NBER08/CanSat_Devboard/HTML/images/cat_pdf_drill_map_CanSat_Devboard-PTH_drill_map.png

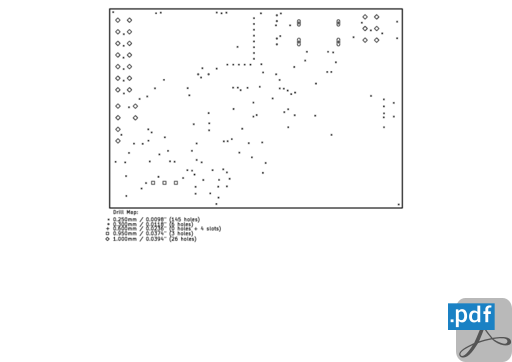
HTML/images/cat_pdf_drill_map_CanSat_Devboard-PTH_drill_map.png
