NBER08/CanSat_Devboard/HTML/images/cat_png_3d_viewer_bottom_CanSat_Devboard-bottom.png

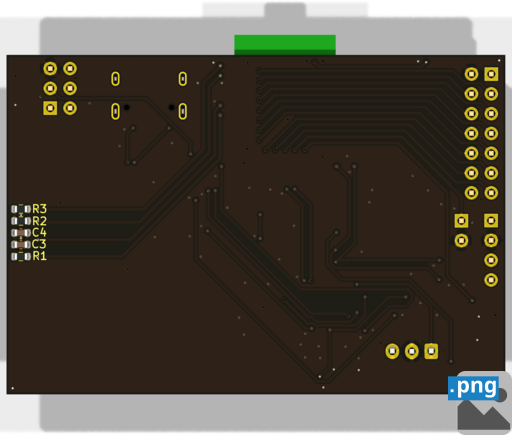
HTML/images/cat_png_3d_viewer_bottom_CanSat_Devboard-bottom.png
