NBER08/CanSat_Devboard/Manufacturing/Fabrication/CanSat_Devboard-fabrication.pdf

# Top Fabrication (Scale 1:1)

# CanSat Devboard Fabrication Document

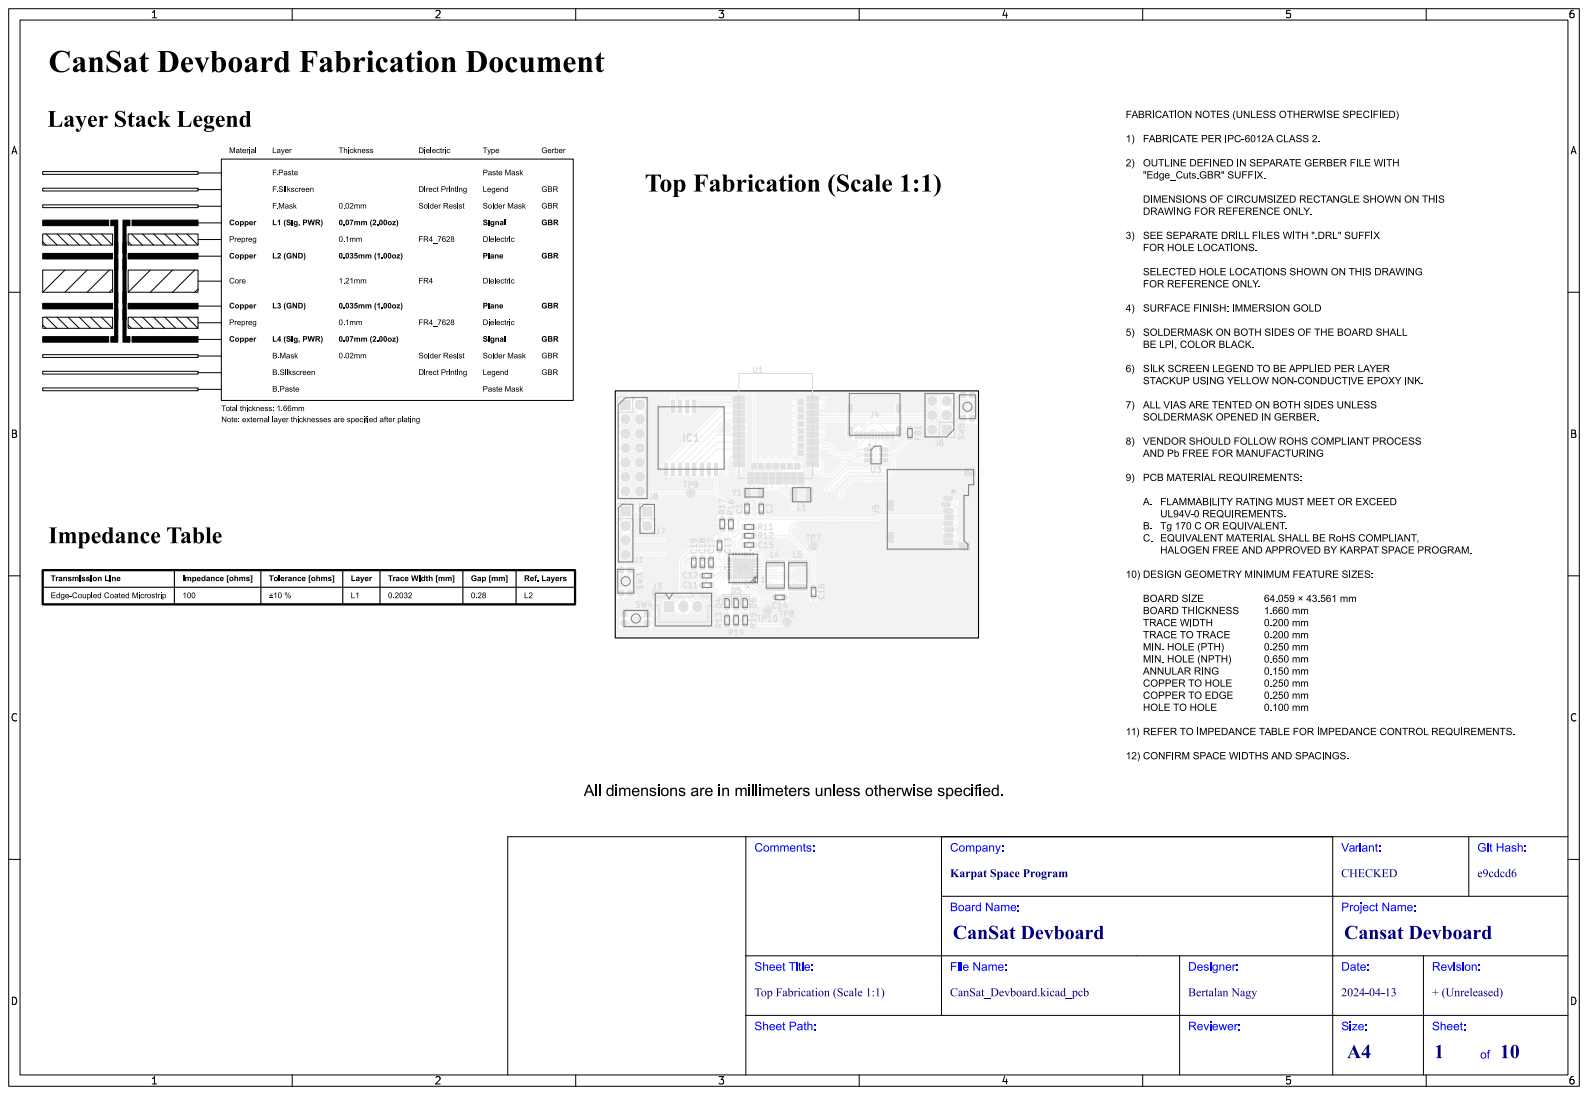
[picture p10: page 1]

# Bottom Fabrication (Scale 1:1)

# CanSat Devboard Fabrication Document

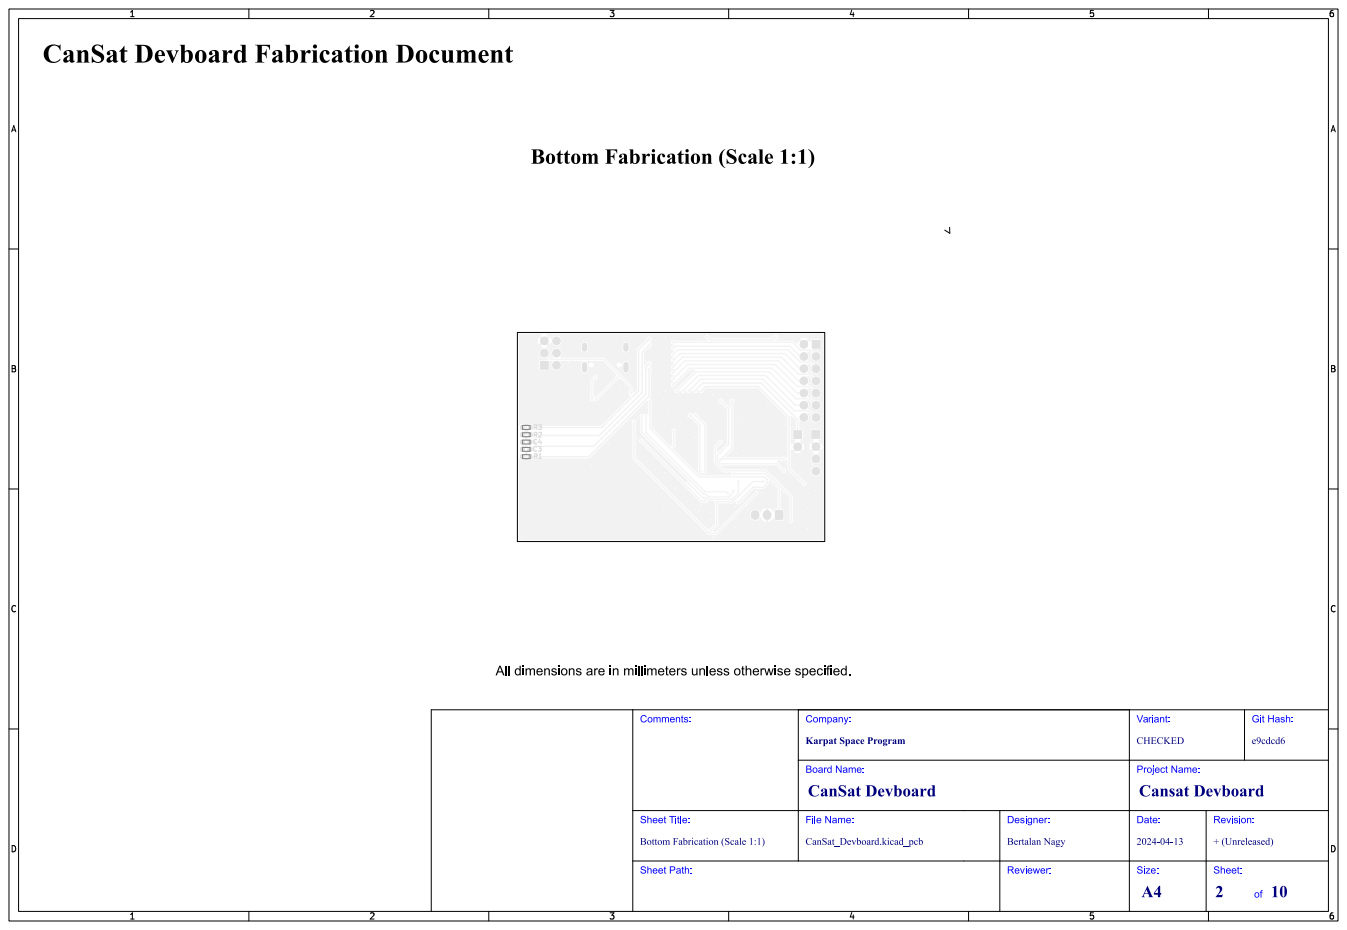
[picture p11: page 2]
Git; Hash:; e9cdcd6; Comments:; Sheet Path:; Sheet Title:; File Name:; CanSat Devboard; Cansat Devboard; Company:; CHECKED; Variant:; Board Name:; CanSat_Devboard.kicad_pcb; Bertalan Nagy; Designer:; Reviewer:; Project Name:; Date:; + (Unreleased); Revision:; Size:; Sheet:

Karpat Space Program

Bottom Fabrication (Scale 1:1)

# Drill Drawing L1 - L4 (Scale 1:1)

# CanSat Devboard Fabrication Document

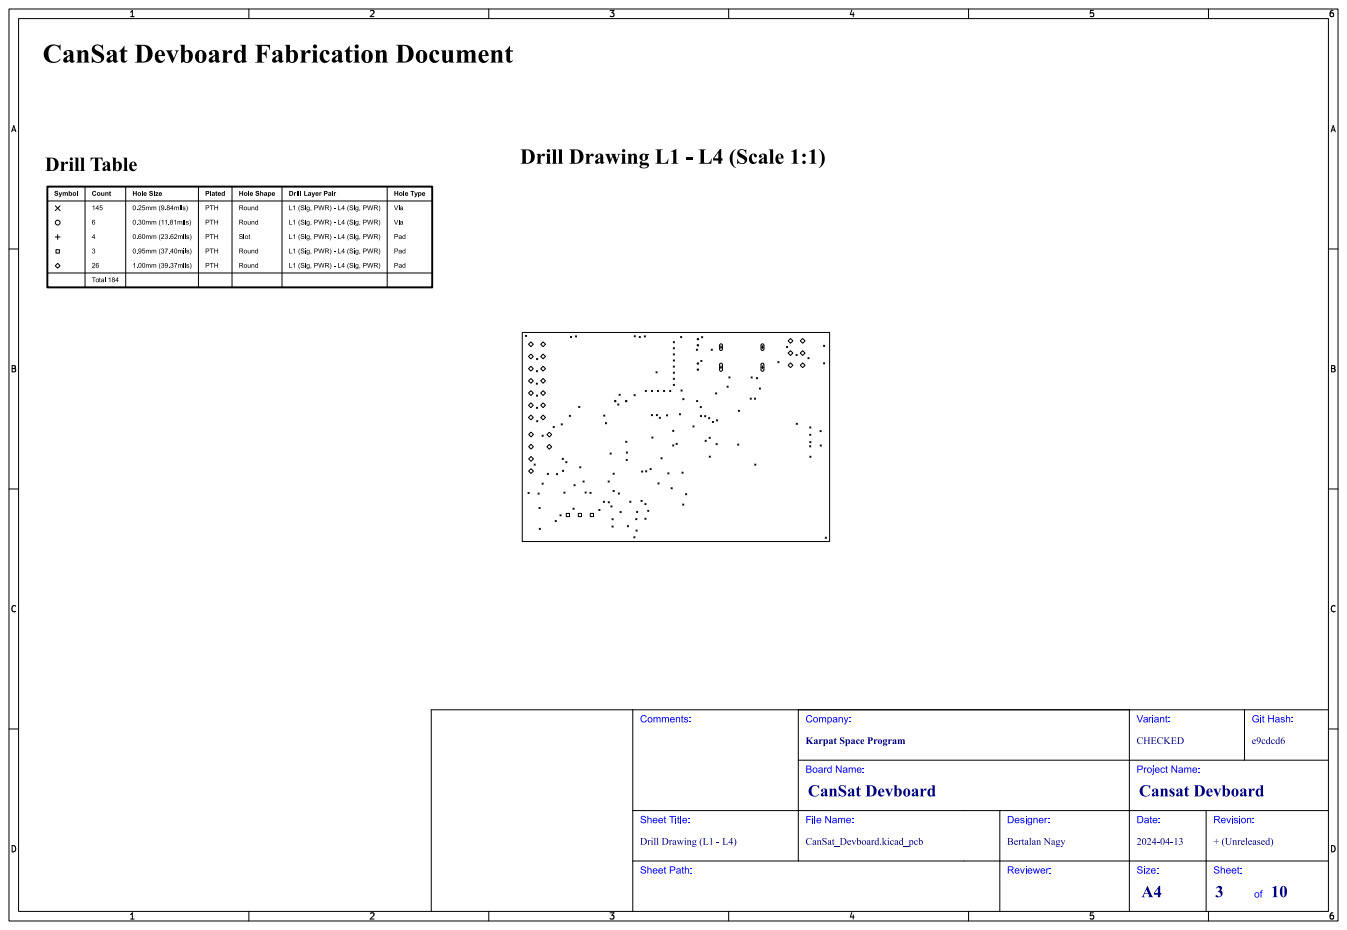
[picture p12: page 3]
Git; Hash:; e9cdcd6; Comments:; Drill Drawing (L1 - L4); Sheet Path:; Sheet Title:; File Name:; CanSat Devboard; Cansat Devboard; Company:; CHECKED; Variant:; Board Name:; CanSat_Devboard.kicad_pcb; Bertalan Nagy; Designer:; Reviewer:; Project Name:; Date:; + (Unreleased); Revision:; Size:; Sheet:

Karpat Space Program

# Drill Drawing L1 - L4 (Scale 1:1)

# CanSat Devboard Fabrication Document

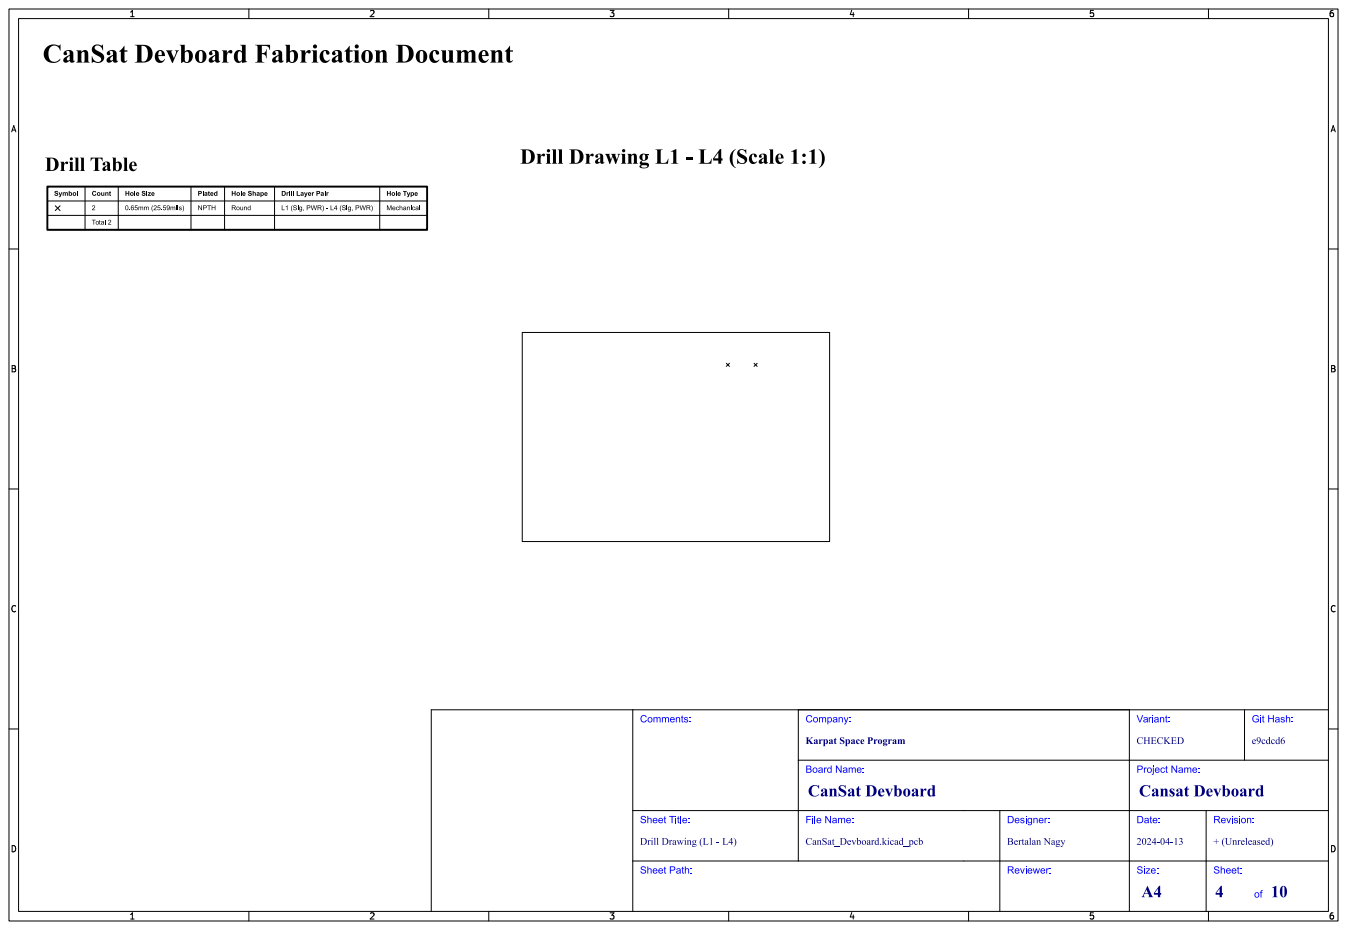
[picture p13: page 4]
Git; Hash:; e9cdcd6; Comments:; Drill Drawing (L1 - L4); Sheet Path:; Sheet Title:; File Name:; CanSat Devboard; Cansat Devboard; Company:; CHECKED; Variant:; Board Name:; CanSat_Devboard.kicad_pcb; Bertalan Nagy; Designer:; Reviewer:; Project Name:; Date:; + (Unreleased); Revision:; Size:; Sheet:

Karpat Space Program

# Top Test Points (Scale 1:1)

# CanSat Devboard Fabrication Document

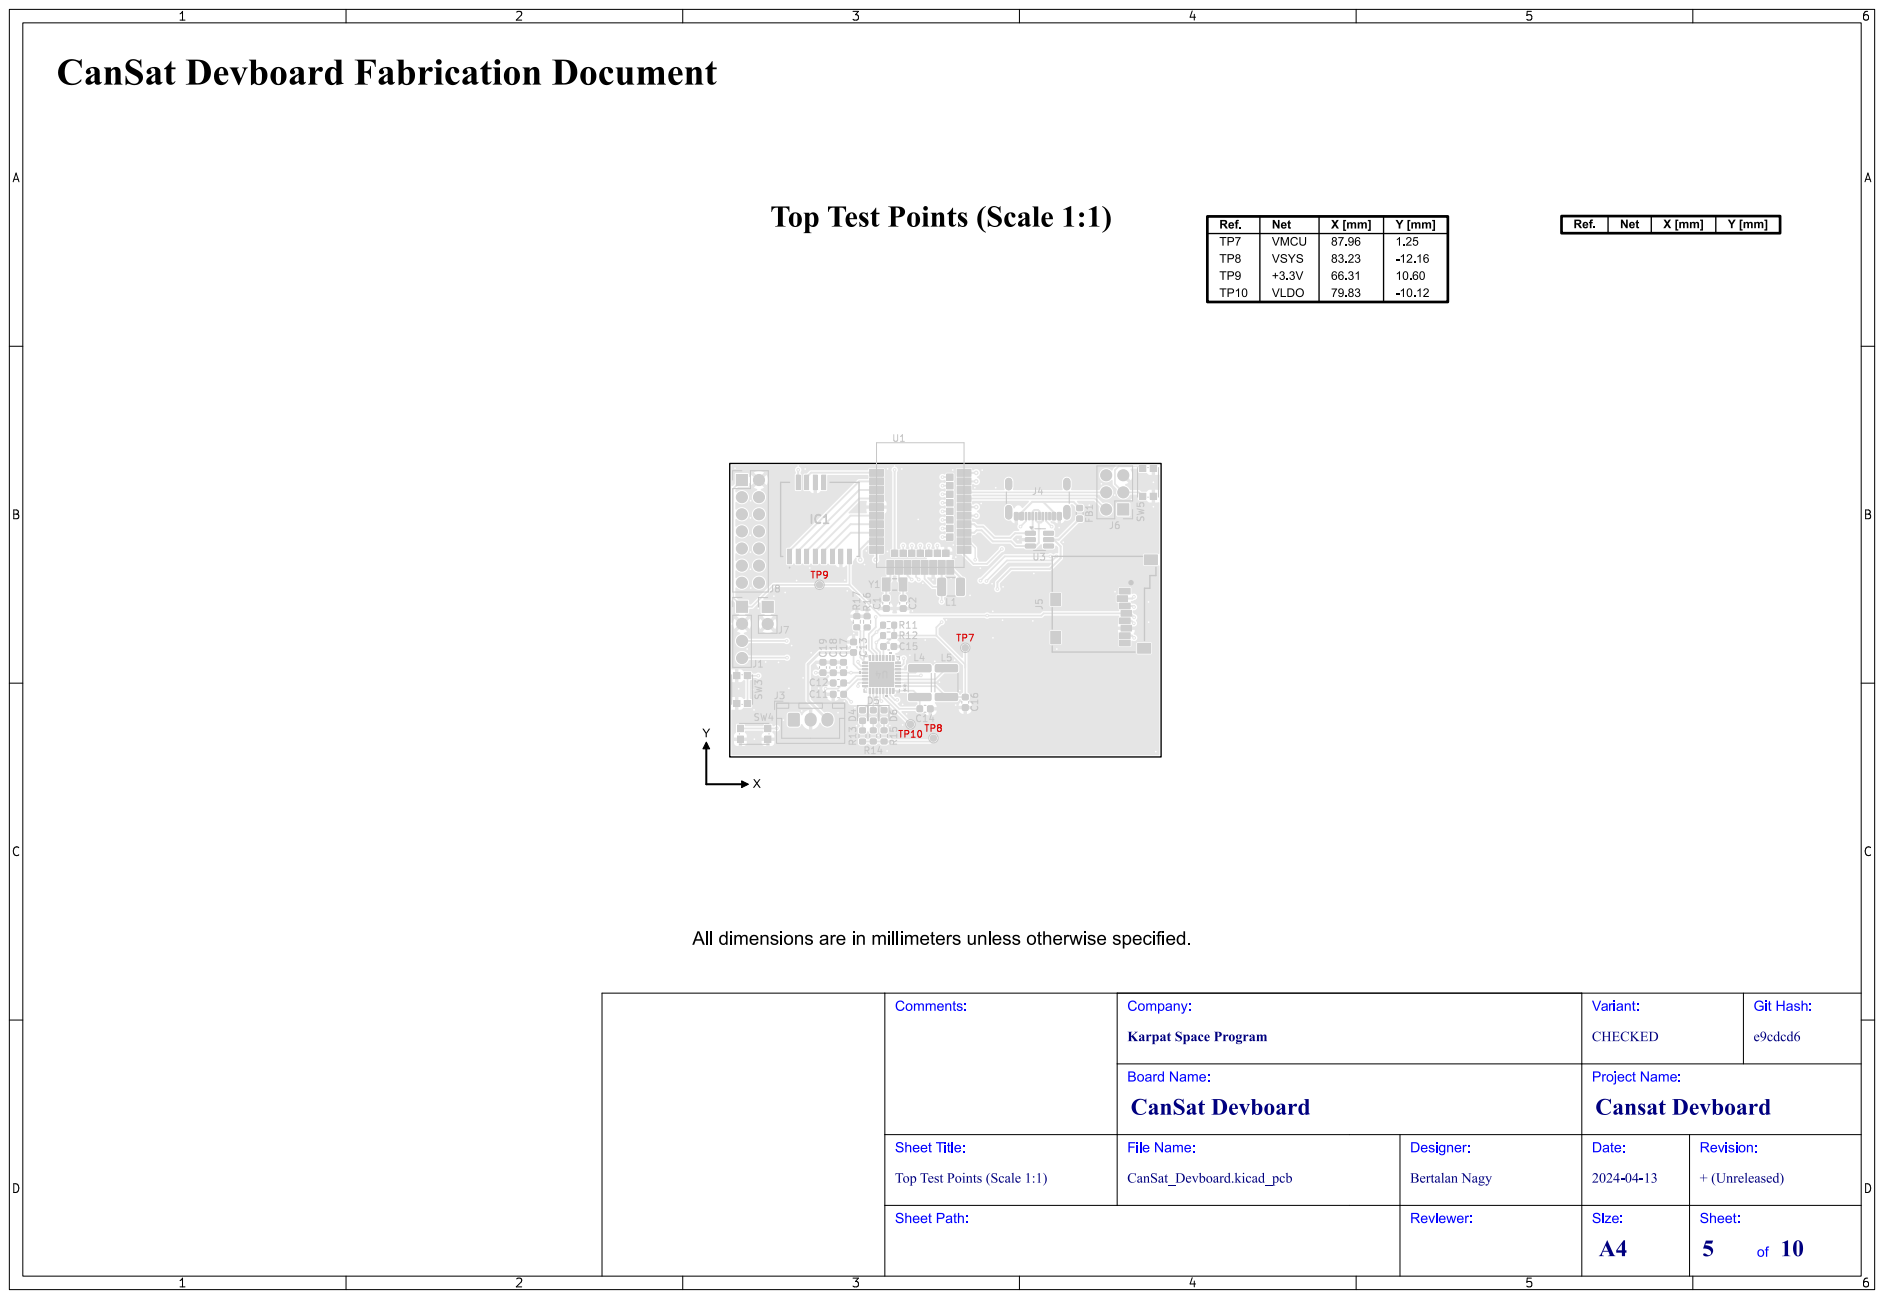
[picture p14: page 5]

Top Test Points (Scale 1:1)

# Bottom Test Points (Scale 1:1)

# CanSat Devboard Fabrication Document

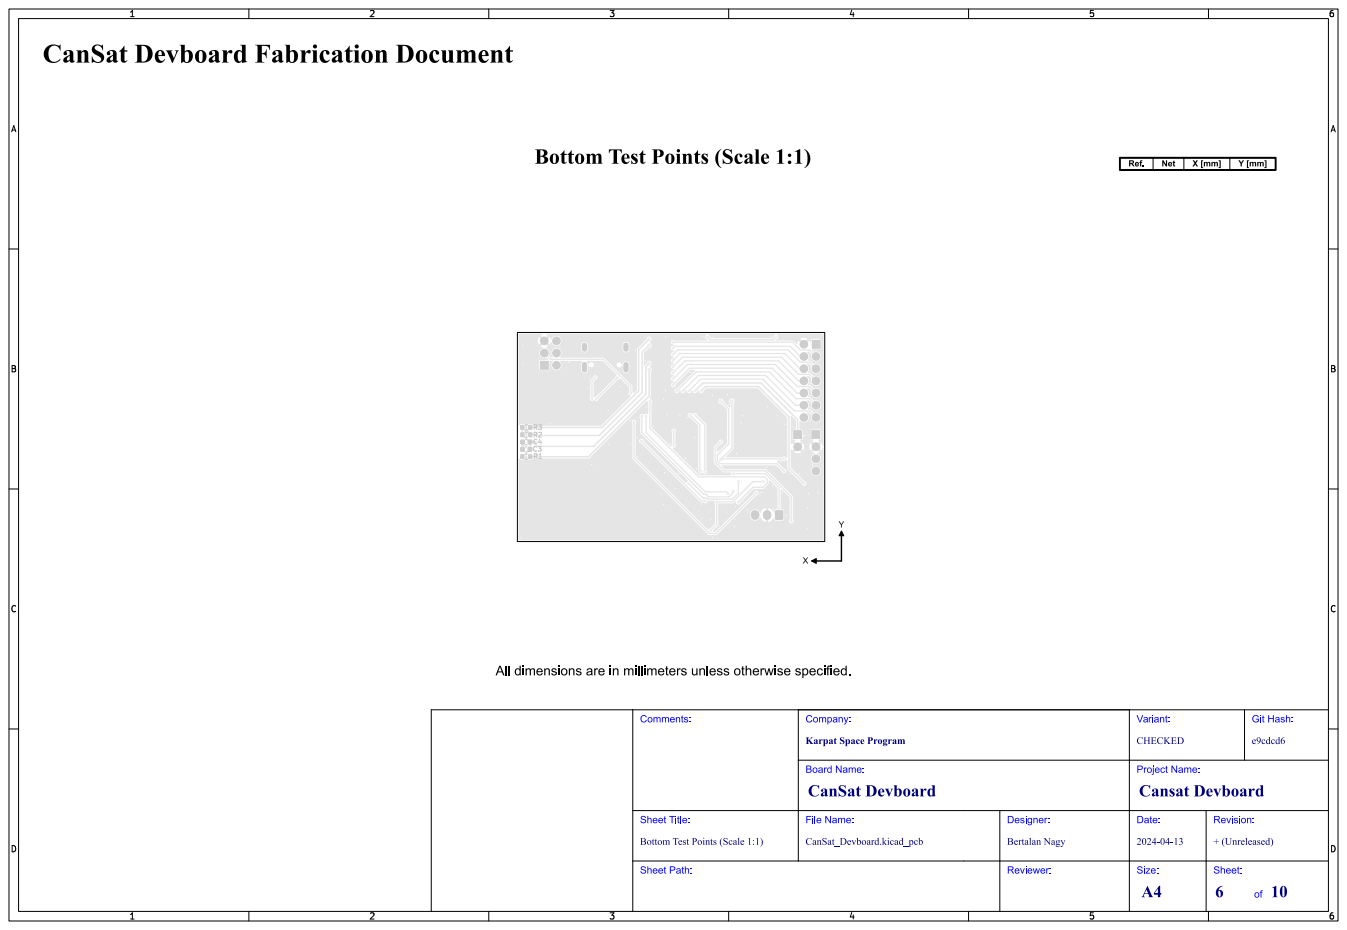
[picture p15: page 6]
Git; Hash:; e9cdcd6; Comments:; Sheet Path:; Sheet Title:; File Name:; CanSat Devboard; Cansat Devboard; Company:; CHECKED; Variant:; Board Name:; CanSat_Devboard.kicad_pcb; Bertalan Nagy; Designer:; Reviewer:; Project Name:; Date:; + (Unreleased); Revision:; Size:; Sheet:

Karpat Space Program

Bottom Test Points (Scale 1:1)

# L1 (Sig, PWR) (Scale 1:1)

# CanSat Devboard Fabrication Document

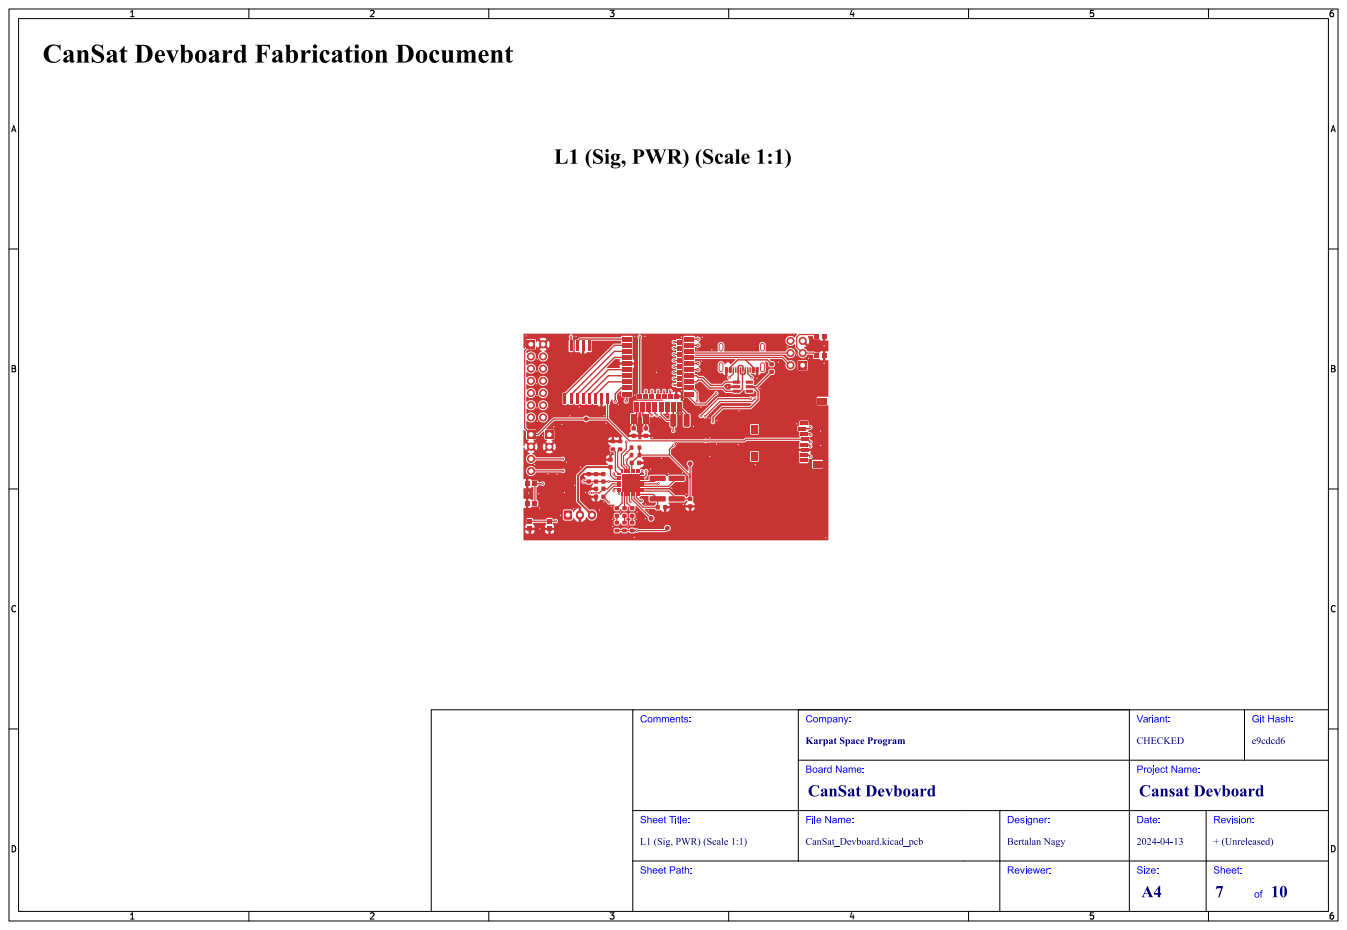
[picture p16: page 7]
Git; Hash:; e9cdcd6; Comments:; Sheet Path:; Sheet Title:; File Name:; CanSat Devboard; Cansat Devboard; Company:; CHECKED; Variant:; Board Name:; CanSat_Devboard.kicad_pcb; Bertalan Nagy; Designer:; Reviewer:; Project Name:; Date:; + (Unreleased); Revision:; Size:; Sheet:

Karpat Space Program

L1 (Sig, PWR) (Scale 1:1)

# L2 (GND) (Scale 1:1)

# CanSat Devboard Fabrication Document

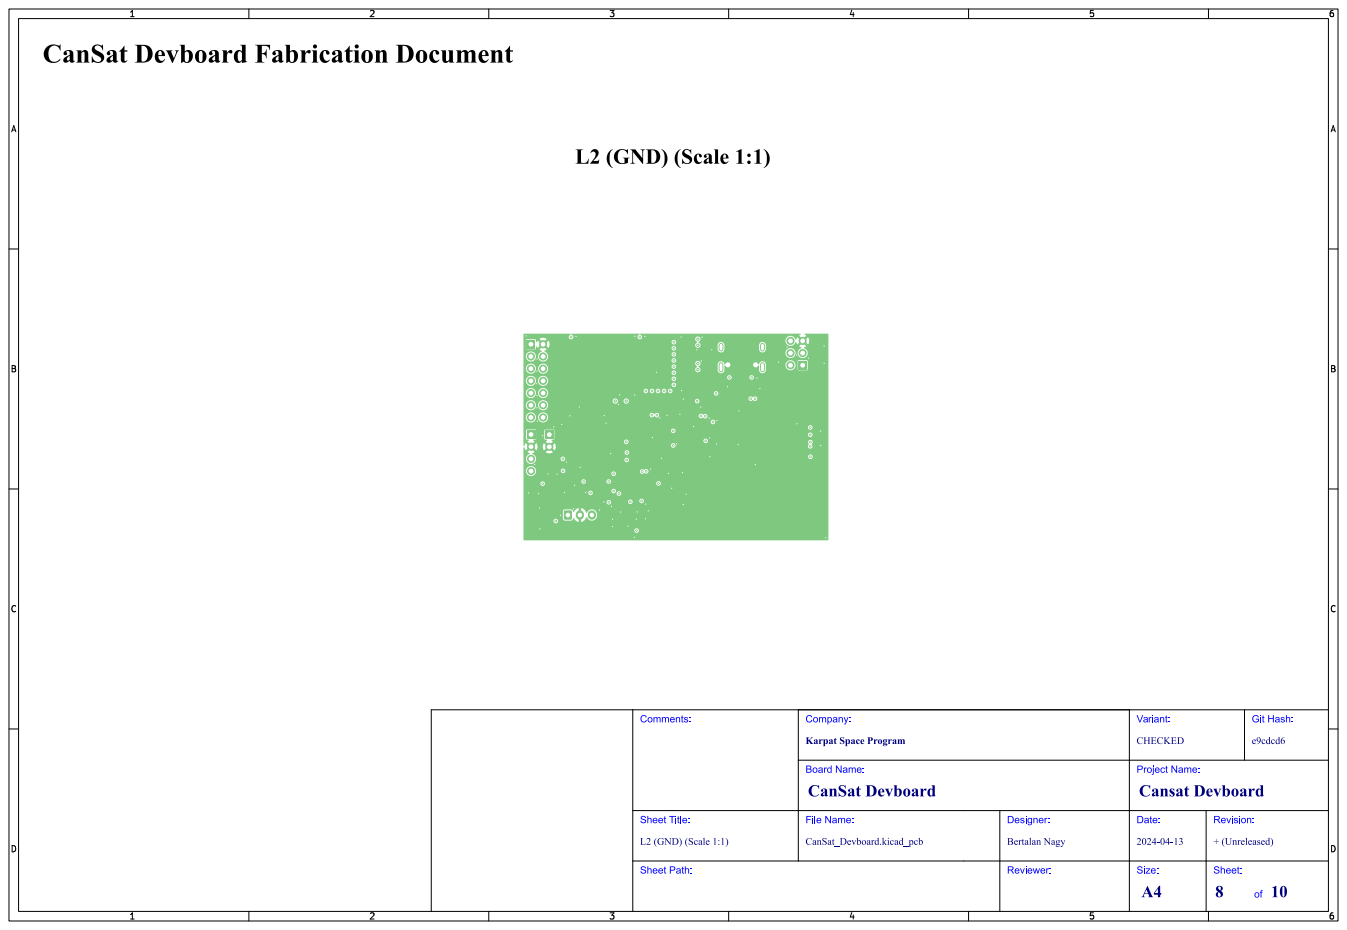
[picture p17: page 8]
Git; Hash:; e9cdcd6; Comments:; L2 (GND) (Scale 1:1); Sheet Path:; Sheet Title:; File Name:; CanSat Devboard; Cansat Devboard; Company:; CHECKED; Variant:; Board Name:; CanSat_Devboard.kicad_pcb; Bertalan Nagy; Designer:; Reviewer:; Project Name:; Date:; + (Unreleased); Revision:; Size:; Sheet:

Karpat Space Program

# L3 (GND) (Scale 1:1)

# CanSat Devboard Fabrication Document

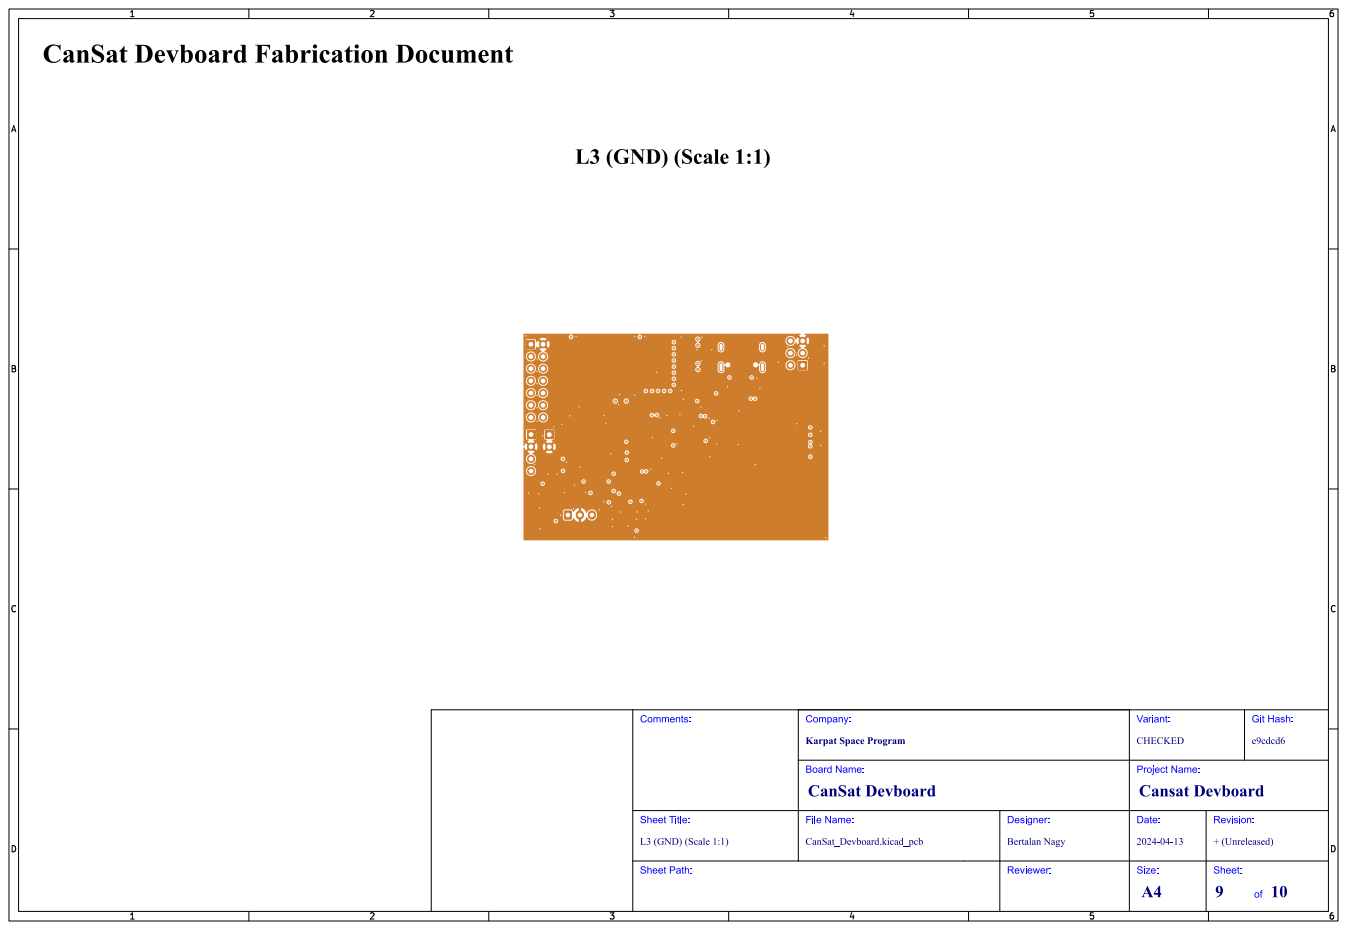
[picture p18: page 9]
Git; Hash:; e9cdcd6; Comments:; L3 (GND) (Scale 1:1); Sheet Path:; Sheet Title:; File Name:; CanSat Devboard; Cansat Devboard; Company:; CHECKED; Variant:; Board Name:; CanSat_Devboard.kicad_pcb; Bertalan Nagy; Designer:; Reviewer:; Project Name:; Date:; + (Unreleased); Revision:; Size:; Sheet:

Karpat Space Program

# L4 (Sig, PWR) (Scale 1:1)

# CanSat Devboard Fabrication Document

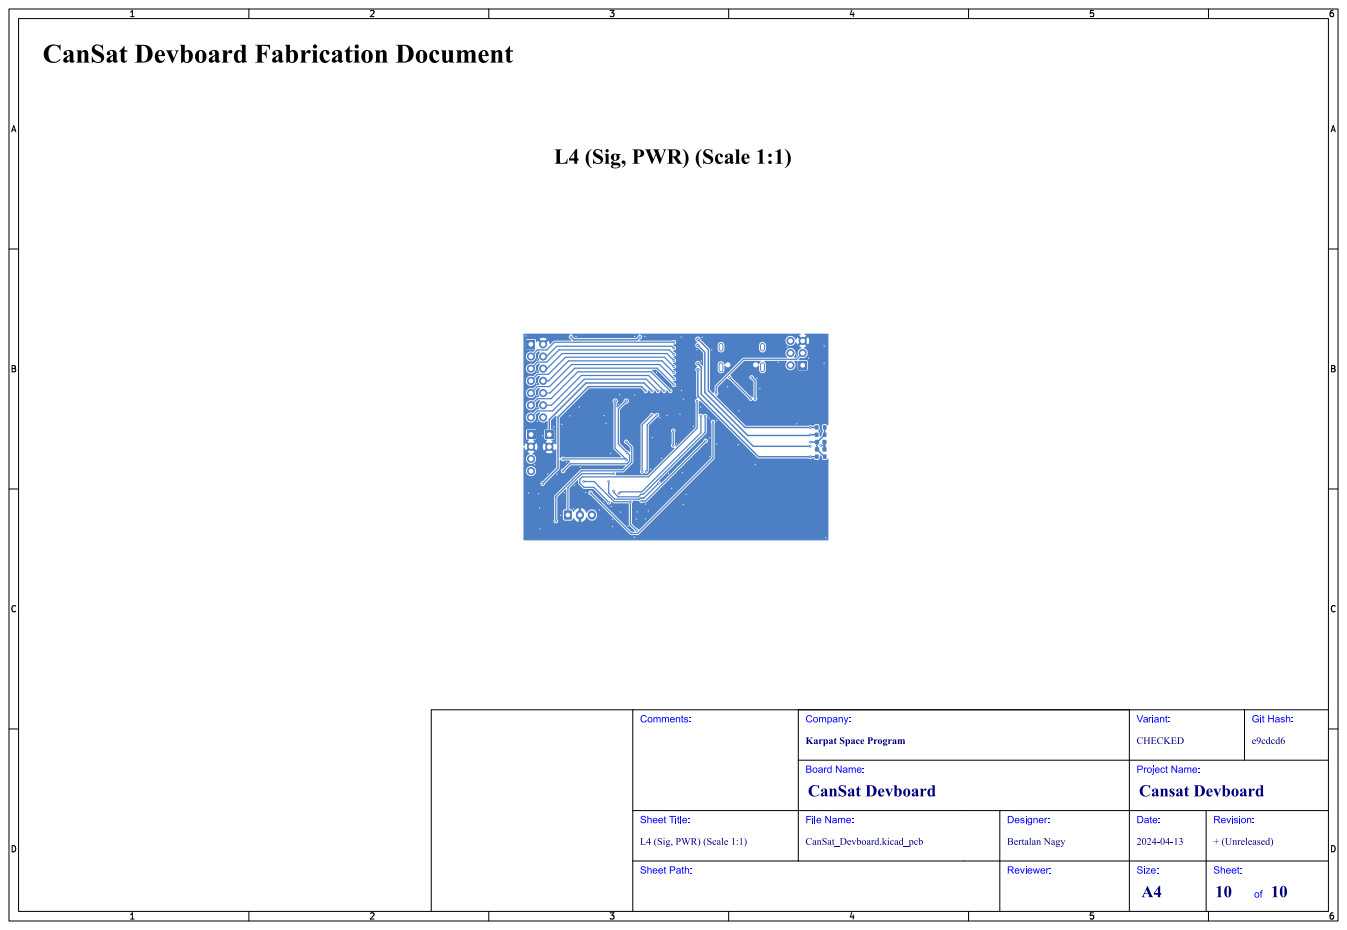
[picture p19: page 10]
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

Karpat Space Program

L4 (Sig, PWR) (Scale 1:1)
