NBER08/CanSat_Devboard/Manufacturing/Fabrication/Gerbers/CanSat_Devboard-NPTH_drill_map.pdf

Drill Map:
0.650mm / 0.0256" (2 holes) (not plated)
