NBER08/CanSat_Devboard/Manufacturing/Assembly/CanSat_Devboard-assembly-3.pdf

# Bottom Assembly (Scale 1:1)

# CanSat Devboard Assembly Document

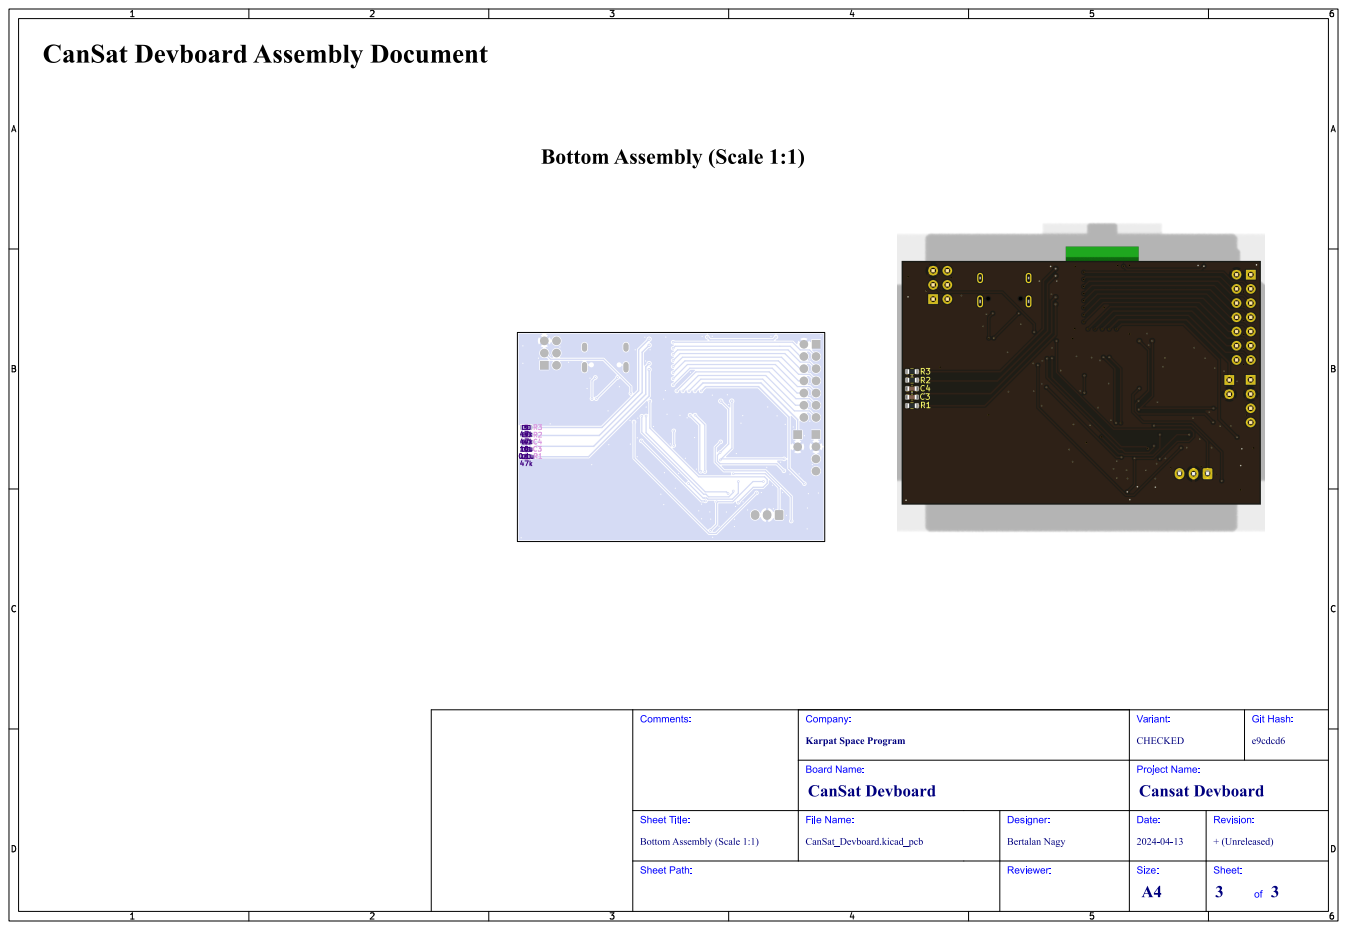
[picture p36: page 1]
Git; Hash:; e9cdcd6; Comments:; Sheet Path:; Sheet Title:; File Name:; CanSat Devboard; Cansat Devboard; Company:; CHECKED; Variant:; Board Name:; CanSat_Devboard.kicad_pcb; Bertalan Nagy; Designer:; Reviewer:; Project Name:; Date:; + (Unreleased); Revision:; Size:; Sheet: 3

Karpat Space Program

Bottom Assembly (Scale 1:1)
