NBER08/CanSat_Devboard/Manufacturing/Assembly/CanSat_Devboard-assembly.pdf

# CanSat Devboard Assembly Document

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

Karpat Space Program

Top/Bottom View

# Top Assembly (Scale 1:1)

# CanSat Devboard Assembly Document


# Bottom Assembly (Scale 1:1)

# CanSat Devboard Assembly Document

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

Karpat Space Program

Bottom Assembly (Scale 1:1)
