NBER08/CanSat_Devboard/Manufacturing/Fabrication/CanSat_Devboard-fabrication-6.pdf

# Bottom Test Points (Scale 1:1)

# CanSat Devboard Fabrication Document

Git; Hash:; e9cdcd6; Comments:; Sheet Path:; Sheet Title:; File Name:; CanSat Devboard; Cansat Devboard; Company:; CHECKED; Variant:; Board Name:; CanSat_Devboard.kicad_pcb; Bertalan Nagy; Designer:; Reviewer:; Project Name:; Date:; + (Unreleased); Revision:; Size:; Sheet: 6

Karpat Space Program

Bottom Test Points (Scale 1:1)
