NBER08/CanSat_Devboard/Manufacturing/Fabrication/CanSat_Devboard-fabrication-7.pdf

# L1 (Sig, PWR) (Scale 1:1)

# CanSat Devboard Fabrication Document

Git; Hash:; e9cdcd6; Comments:; Sheet Path:; Sheet Title:; File Name:; CanSat Devboard; Cansat Devboard; Company:; CHECKED; Variant:; Board Name:; CanSat_Devboard.kicad_pcb; Bertalan Nagy; Designer:; Reviewer:; Project Name:; Date:; + (Unreleased); Revision:; Size:; Sheet: 7

Karpat Space Program

L1 (Sig, PWR) (Scale 1:1)
