NBER08/CanSat_Devboard/Manufacturing/Fabrication/CanSat_Devboard-fabrication-1.pdf

# Top Fabrication (Scale 1:1)

# CanSat Devboard Fabrication Document
