NBER08/CanSat_Devboard/Manufacturing/Fabrication/CanSat_Devboard-fabrication-5.pdf

# Top Test Points (Scale 1:1)

# CanSat Devboard Fabrication Document


Top Test Points (Scale 1:1)
