NBER08/CanSat_Devboard/Manufacturing/Fabrication/Gerbers/CanSat_Devboard-PTH_drill_map.pdf

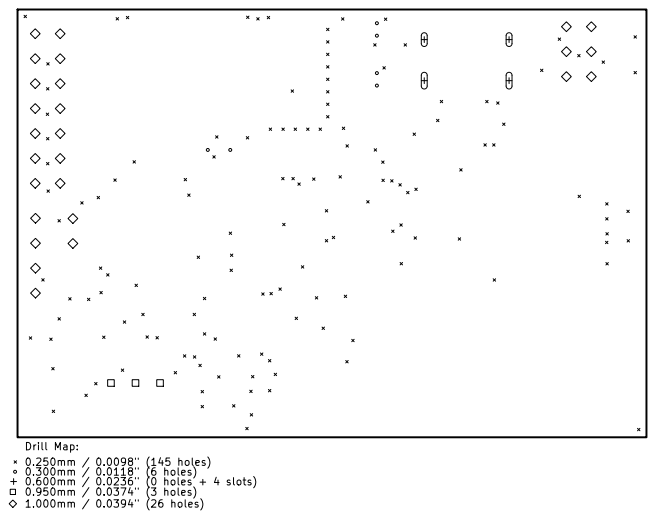
[picture p38: page 1]
